yxbh/GridDogs/renders/anchor_bone.png

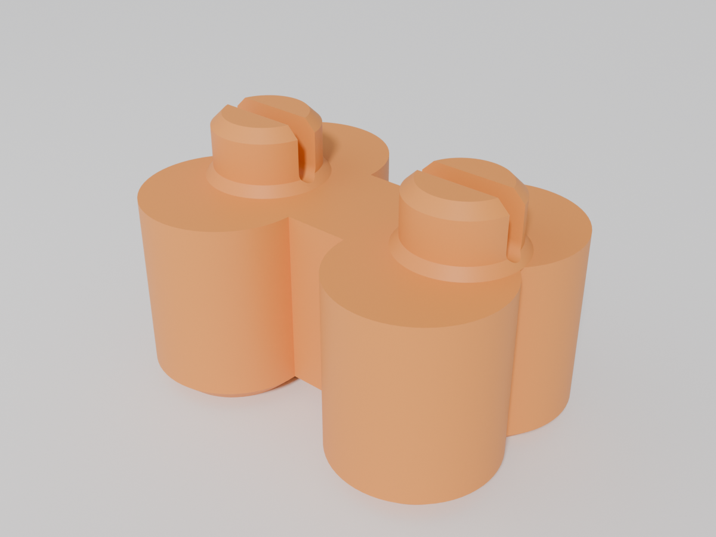
renders/anchor_bone.png
