yxbh/GridDogs/renders/anchor_curve_bowl_20mm.png

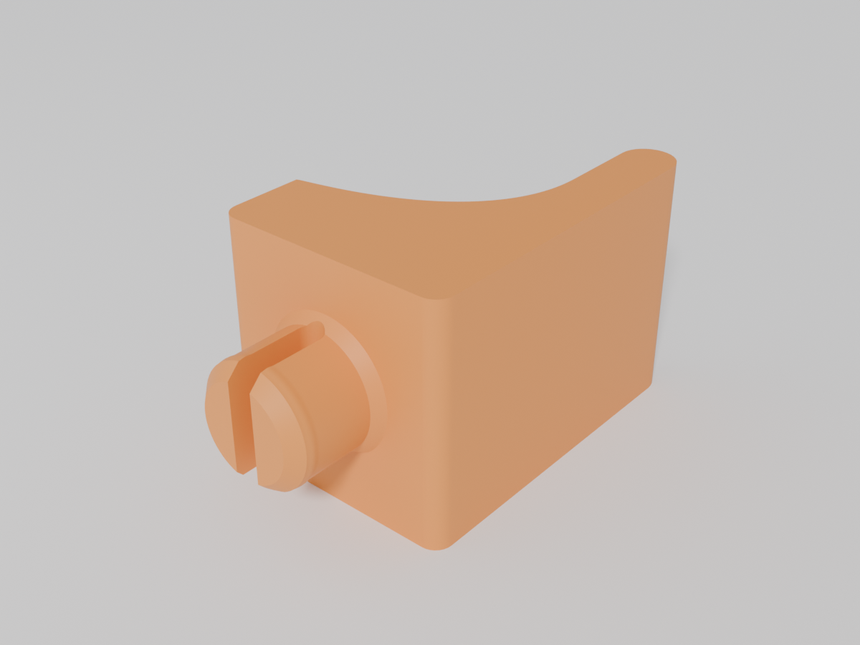
renders/anchor_curve_bowl_20mm.png
