yxbh/GridDogs/renders/anchor_curve_bowl_40mm.png

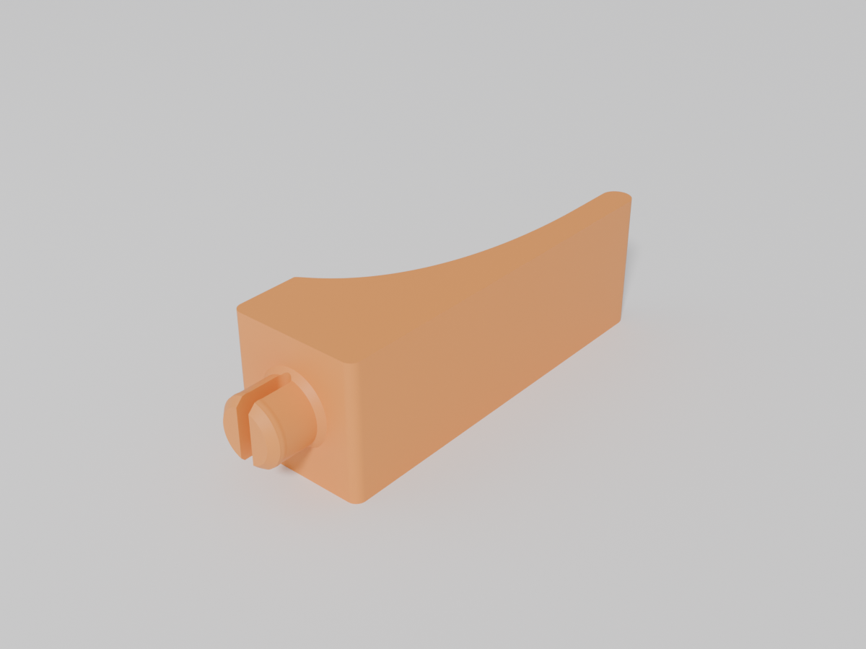
renders/anchor_curve_bowl_40mm.png
