yxbh/GridDogs/renders/anchor_round_bumper_20mm.png

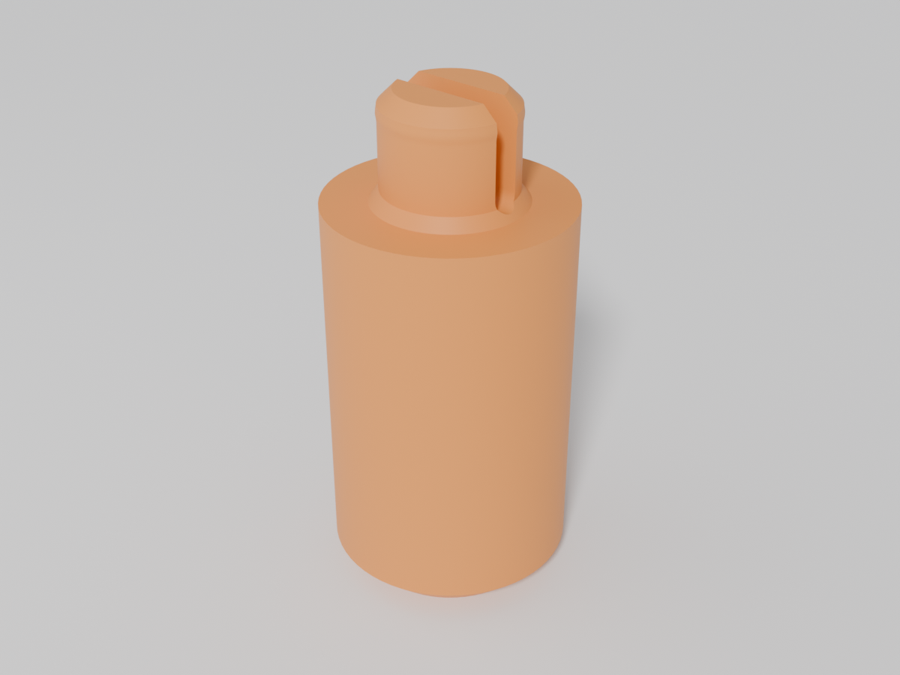
renders/anchor_round_bumper_20mm.png
