yxbh/GridDogs/renders/anchor_round_bumper_40mm.png

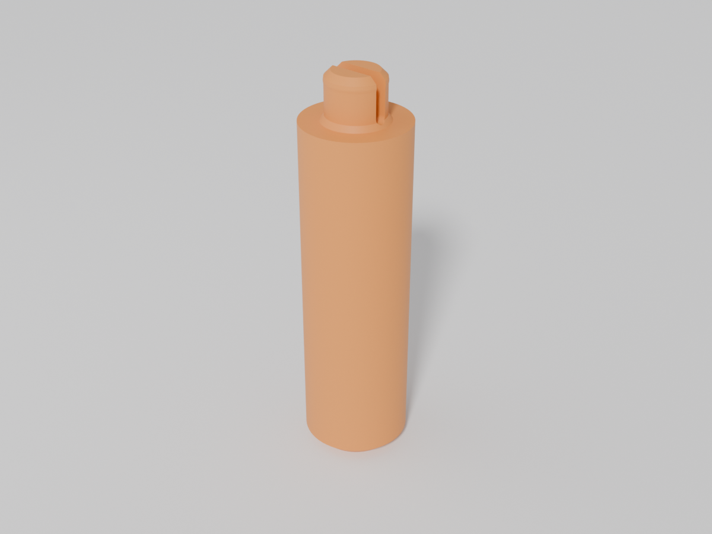
renders/anchor_round_bumper_40mm.png
