yxbh/GridDogs/renders/anchor_wall_diagonal_2x2_20mm.png

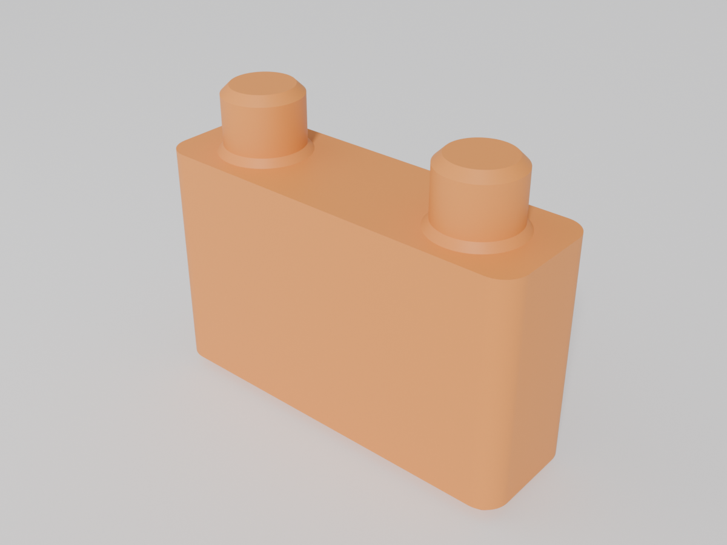
renders/anchor_wall_diagonal_2x2_20mm.png
