yxbh/GridDogs/renders/anchor_wall_diagonal_2x3_40mm.png

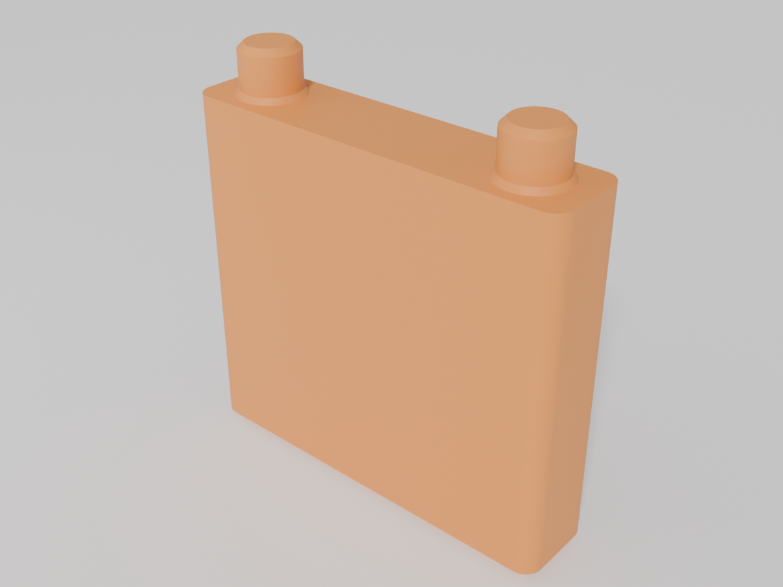
renders/anchor_wall_diagonal_2x3_40mm.png
