yxbh/GridDogs/renders/anchor_wall_long_40mm.png

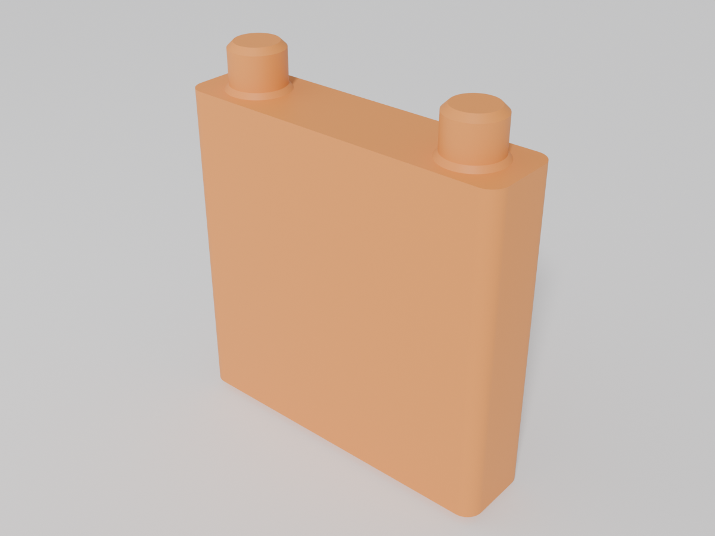
renders/anchor_wall_long_40mm.png
