yxbh/GridDogs/renders/anchor_wall_short_20mm.png

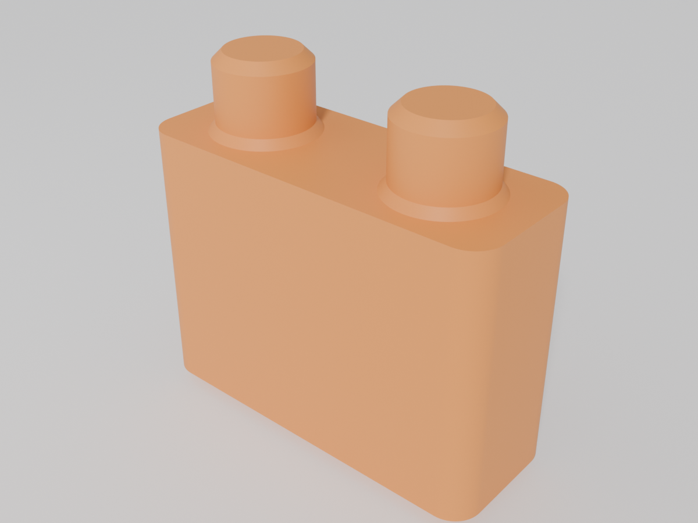
renders/anchor_wall_short_20mm.png
