yxbh/GridDogs/renders/anchor_wall_short_40mm.png

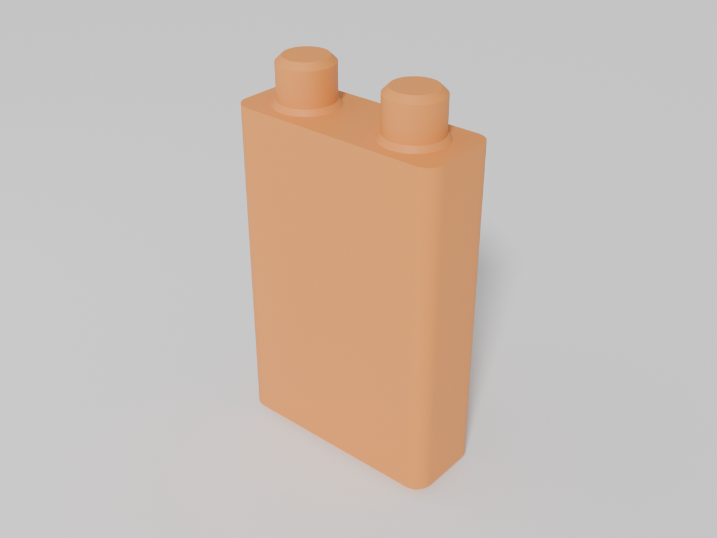
renders/anchor_wall_short_40mm.png
