yxbh/GridDogs/renders/tile_1x1_gridfinity.png

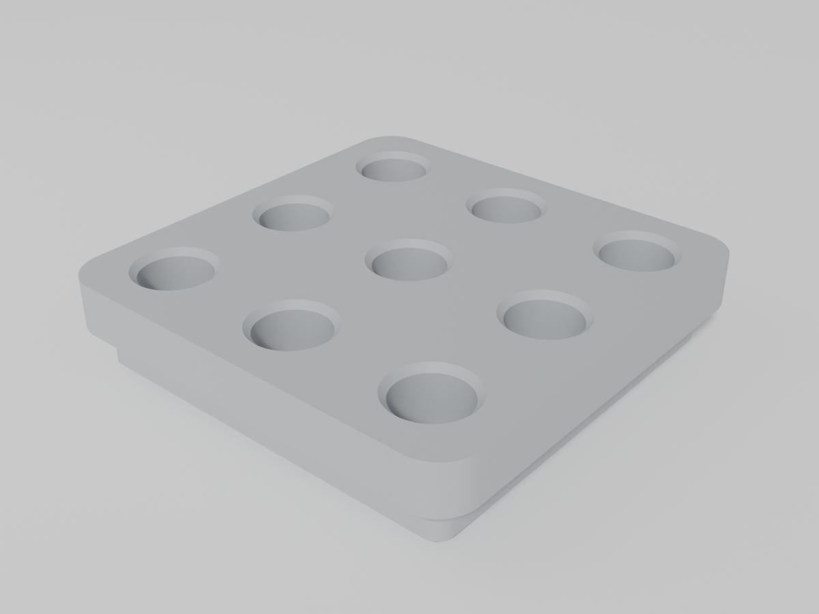
renders/tile_1x1_gridfinity.png
