yxbh/GridDogs/renders/tile_1x3_gridfinity.png

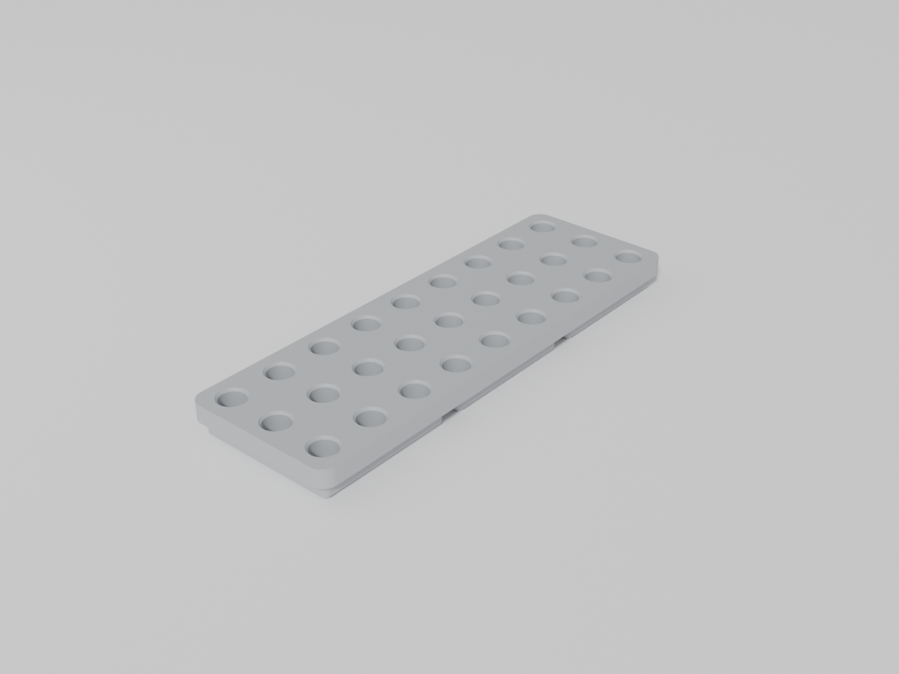
renders/tile_1x3_gridfinity.png
