yxbh/GridDogs/renders/tile_1x7_gridfinity.png

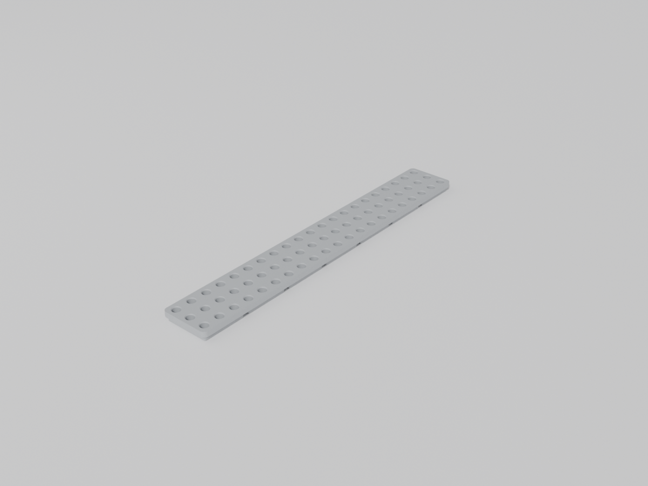
renders/tile_1x7_gridfinity.png
