yxbh/GridDogs/renders/tile_2x2_gridfinity.png

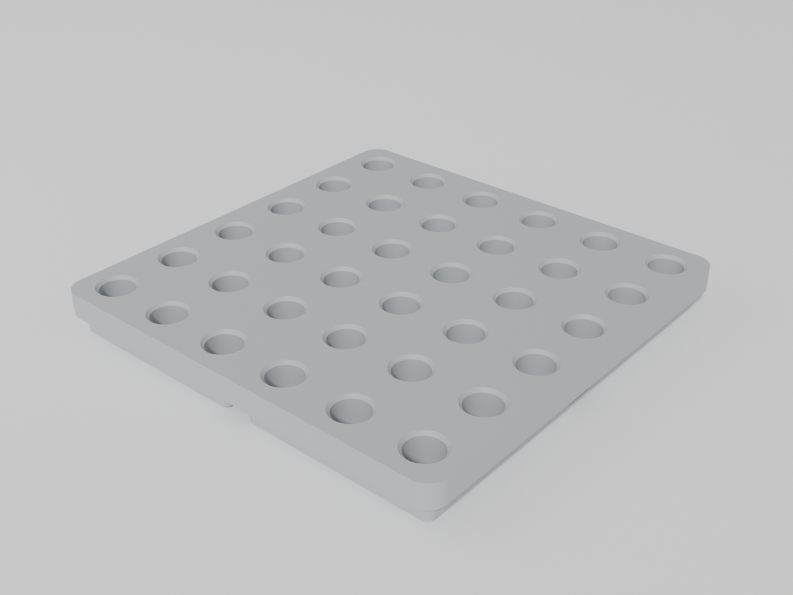
renders/tile_2x2_gridfinity.png
