yxbh/GridDogs/renders/tile_4x4_gridfinity.png

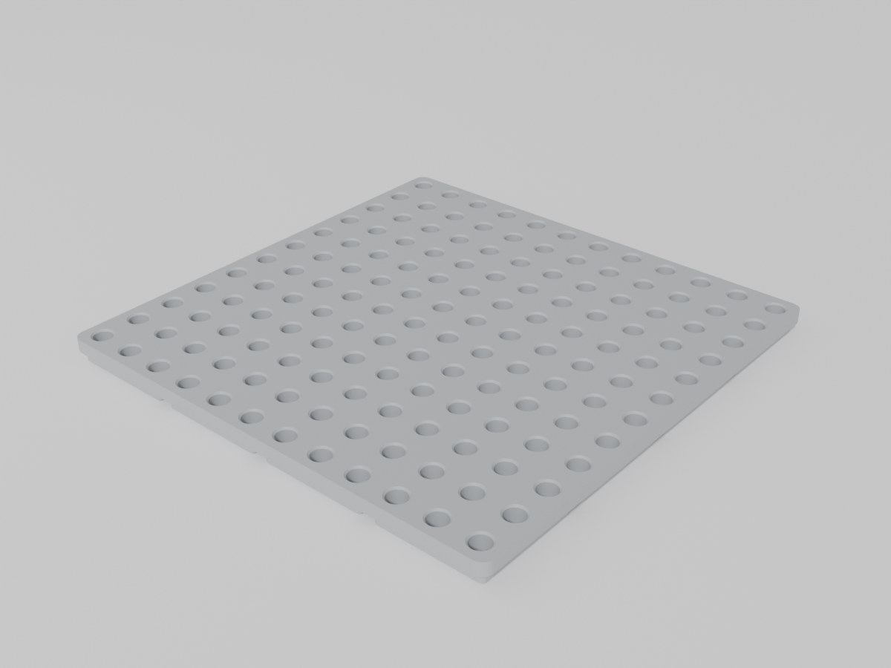
renders/tile_4x4_gridfinity.png
