yxbh/GridDogs/renders/tile_4x7_gridfinity.png

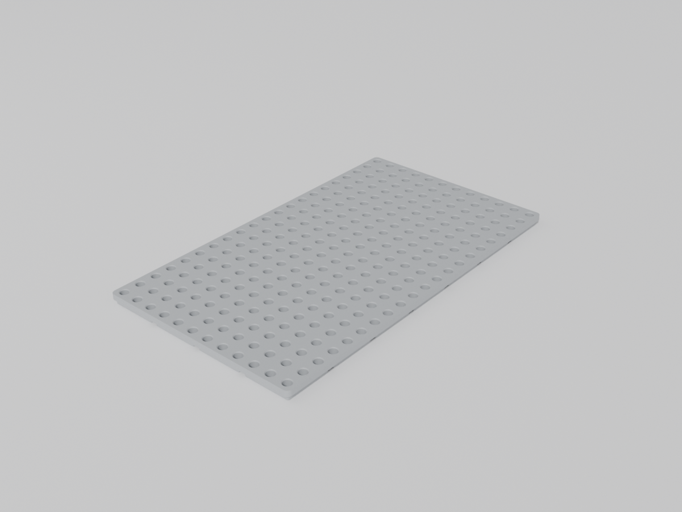
renders/tile_4x7_gridfinity.png
