yxbh/GridDogs/stl/tile_1x1_gridfinity.stl

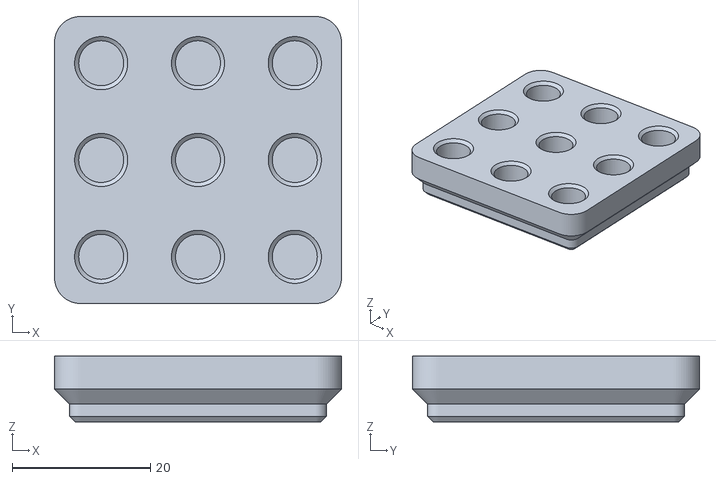
[picture p36: CAD file, 2026-09-03]
stl/tile_1x1_gridfinity.stl
41.5 x 41.5 x 9.50
