yxbh/GridDogs/stl/tile_2x3_gridfinity.stl

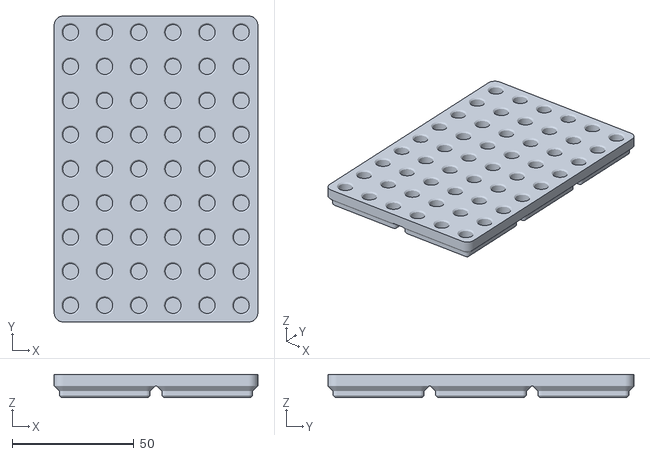
[picture p37: CAD file, 2026-09-03]
stl/tile_2x3_gridfinity.stl
83.5 x 125.5 x 9.50
