yxbh/GridDogs/stl/tile_6x7_gridfinity.stl

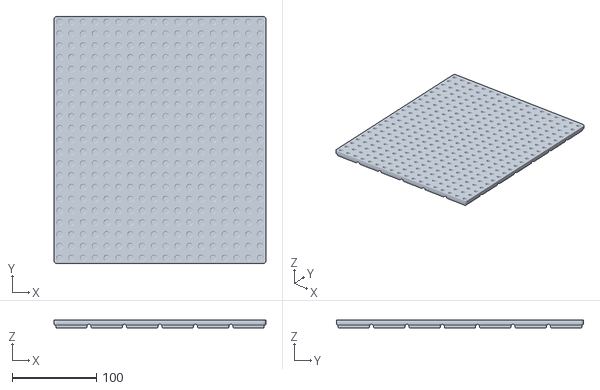
[picture p38: CAD file, 2026-09-03]
stl/tile_6x7_gridfinity.stl
251.5 x 293.5 x 9.50
