yxbh/GridDogs/stl/tile_6x6_gridfinity.stl

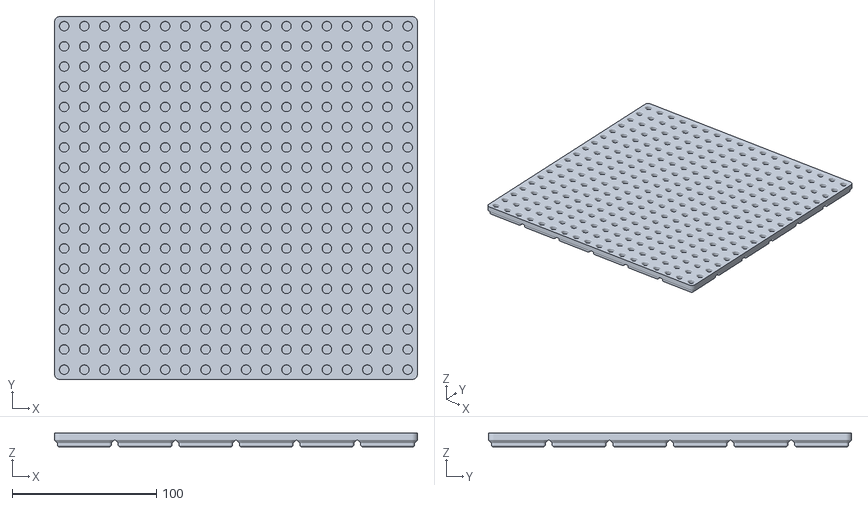
[picture p39: CAD file, 2026-09-03]
stl/tile_6x6_gridfinity.stl
251.5 x 251.5 x 9.50
