yxbh/GridDogs/stl/tile_4x4_gridfinity.stl

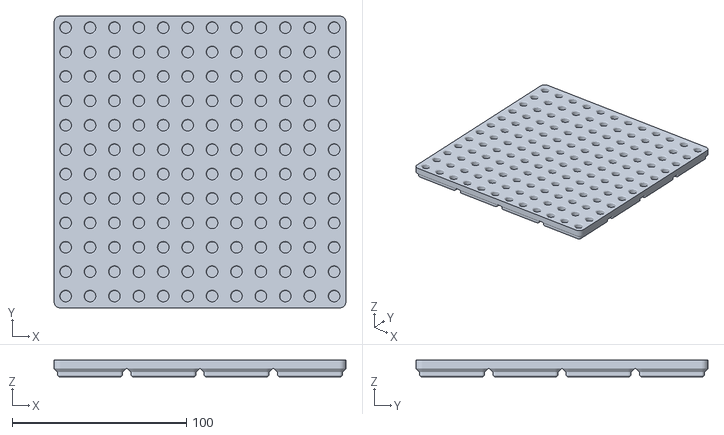
[picture p40: CAD file, 2026-09-03]
stl/tile_4x4_gridfinity.stl
167.5 x 167.5 x 9.50
