yxbh/GridDogs/stl/tile_1x4_gridfinity.stl

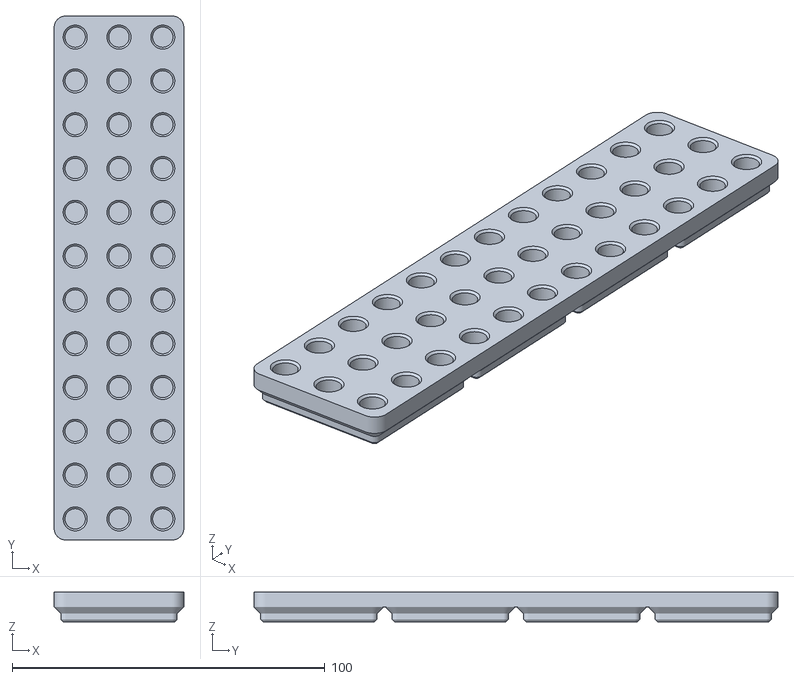
[picture p41: CAD file, 2026-09-03]
stl/tile_1x4_gridfinity.stl
41.5 x 167.5 x 9.50
