yxbh/GridDogs/stl/tile_1x6_gridfinity.stl

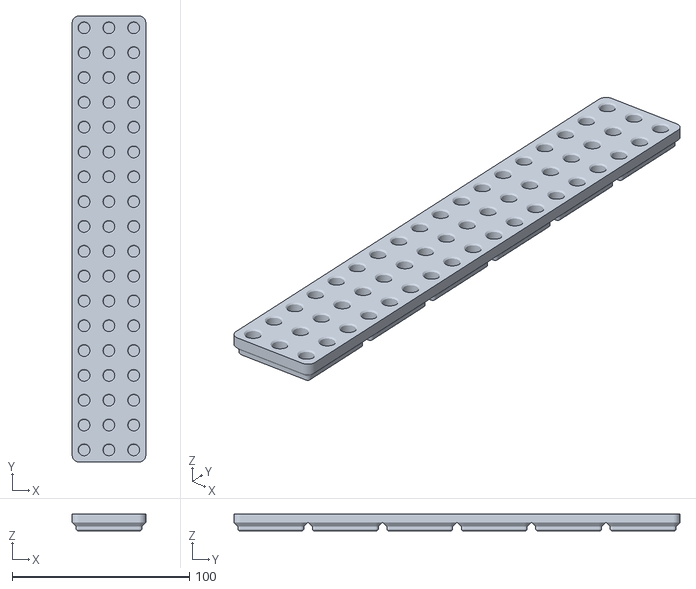
[picture p42: CAD file, 2026-09-03]
stl/tile_1x6_gridfinity.stl
41.5 x 251.5 x 9.50
