yxbh/GridDogs/stl/anchor_round_bumper_40mm.stl

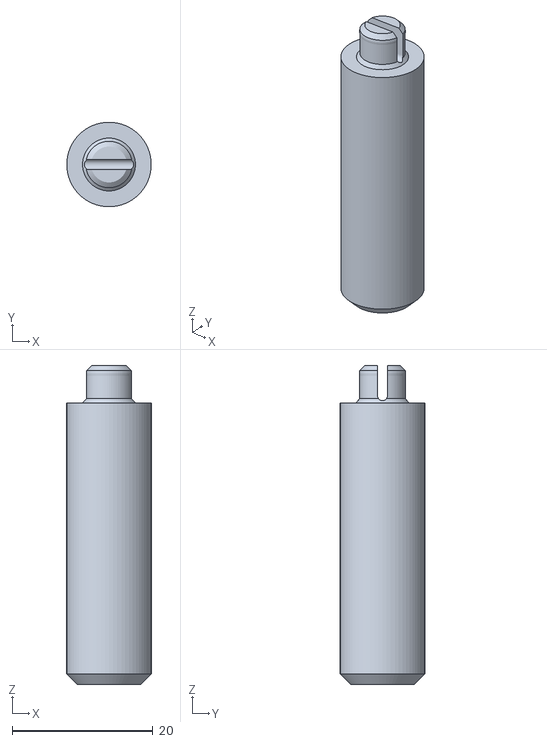
[picture p43: CAD file, 2026-09-03]
stl/anchor_round_bumper_40mm.stl
12.0 x 12.0 x 45.3
