yxbh/GridDogs/stl/tile_1x3_gridfinity.stl

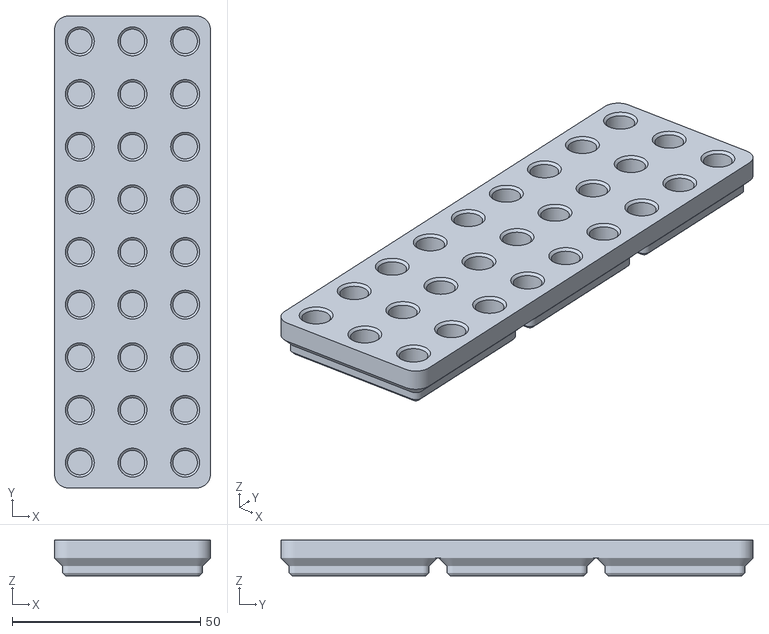
[picture p44: CAD file, 2026-09-03]
stl/tile_1x3_gridfinity.stl
41.5 x 125.5 x 9.50
