yxbh/GridDogs/stl/tile_7x7_gridfinity.stl

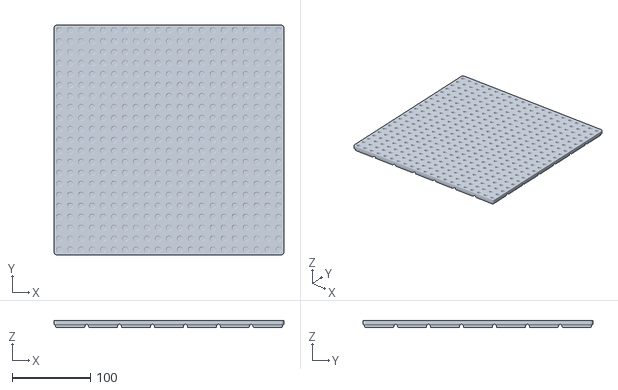
[picture p45: CAD file, 2026-09-03]
stl/tile_7x7_gridfinity.stl
293.5 x 293.5 x 9.50
