yxbh/GridDogs/stl/tile_3x4_gridfinity.stl

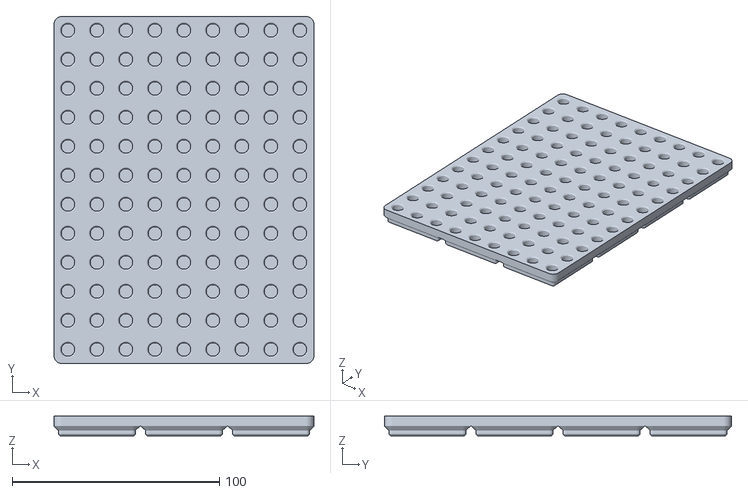
[picture p46: CAD file, 2026-09-03]
stl/tile_3x4_gridfinity.stl
125.5 x 167.5 x 9.50
