yxbh/GridDogs/stl/anchor_round_bumper_20mm.stl

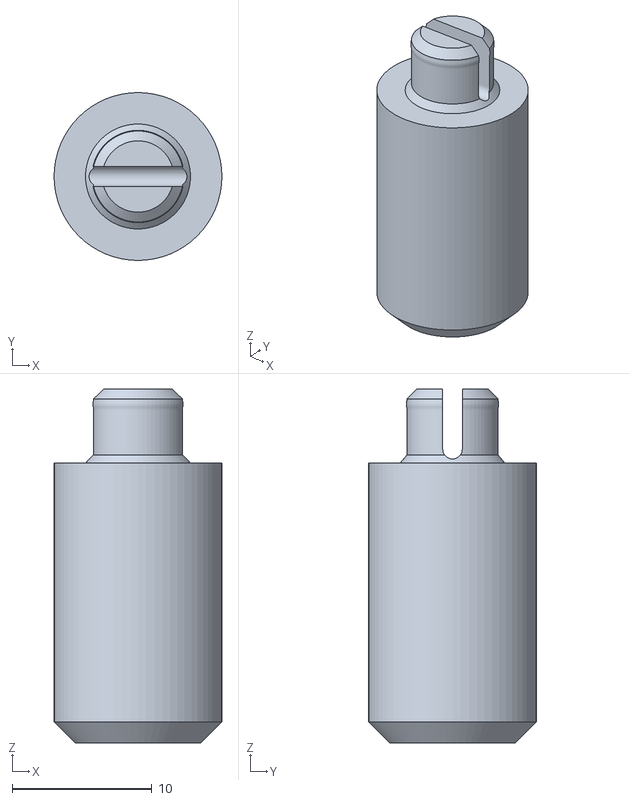
[picture p47: CAD file, 2026-09-03]
stl/anchor_round_bumper_20mm.stl
12.0 x 12.0 x 25.3
