yxbh/GridDogs/stl/tile_3x3_gridfinity.stl

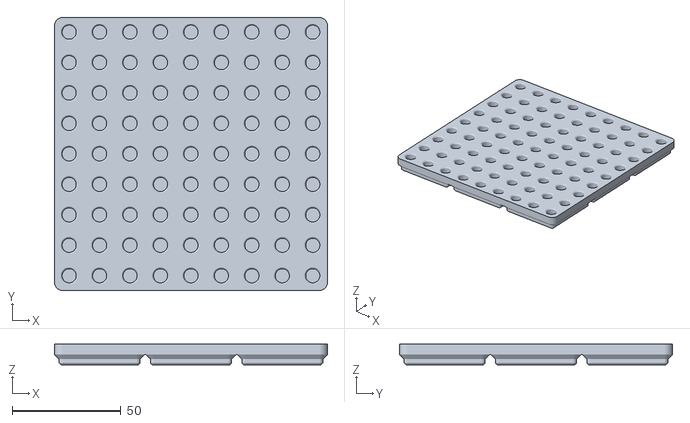
[picture p48: CAD file, 2026-09-03]
stl/tile_3x3_gridfinity.stl
125.5 x 125.5 x 9.50
