yxbh/GridDogs/stl/tile_2x7_gridfinity.stl

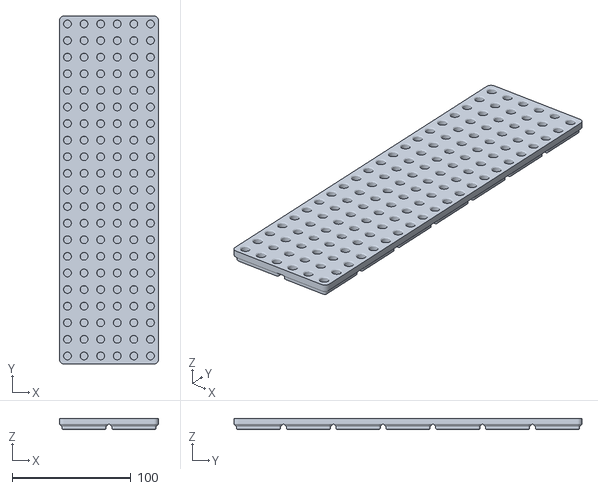
[picture p49: CAD file, 2026-09-03]
stl/tile_2x7_gridfinity.stl
83.5 x 293.5 x 9.50
