yxbh/GridDogs/stl/tile_2x5_gridfinity.stl

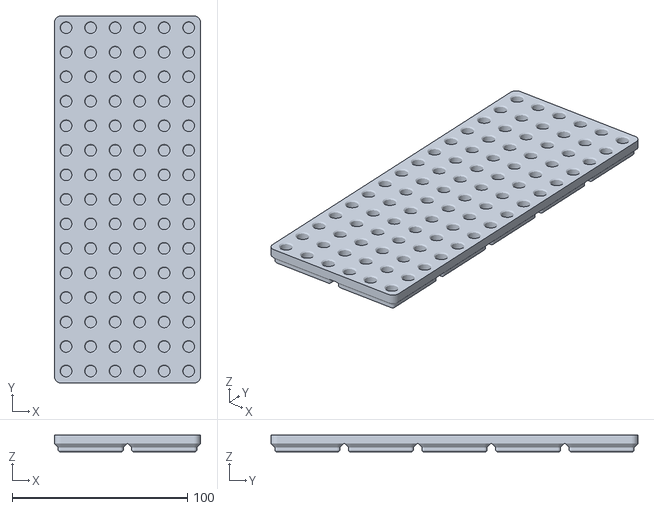
[picture p50: CAD file, 2026-09-03]
stl/tile_2x5_gridfinity.stl
83.5 x 209.5 x 9.50
