yxbh/GridDogs/stl/tile_5x6_gridfinity.stl

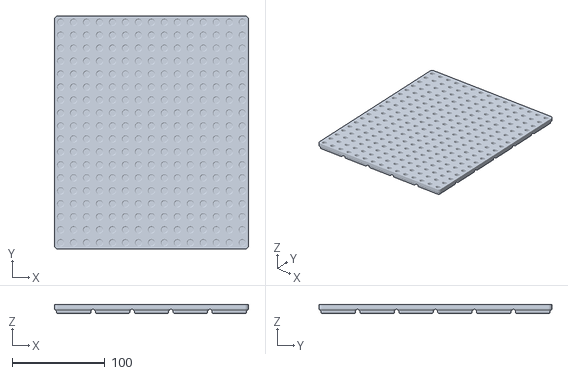
[picture p51: CAD file, 2026-09-03]
stl/tile_5x6_gridfinity.stl
209.5 x 251.5 x 9.50
