yxbh/GridDogs/stl/anchor_wall_long_40mm.stl

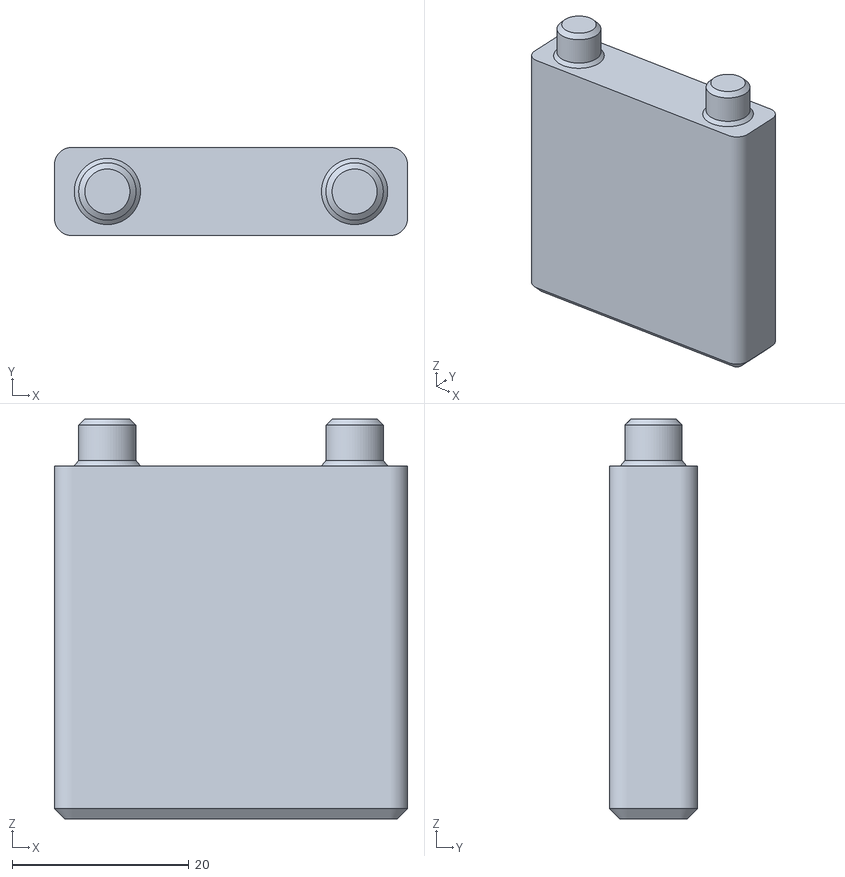
[picture p52: CAD file, 2026-09-03]
stl/anchor_wall_long_40mm.stl
40.0 x 10.0 x 45.3
