yxbh/GridDogs/stl/tile_3x6_gridfinity.stl

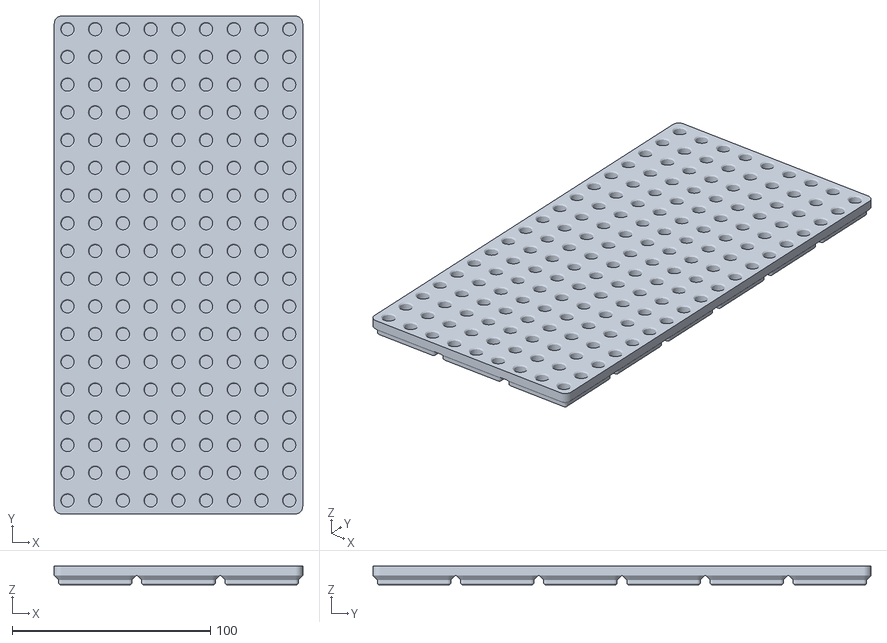
[picture p53: CAD file, 2026-09-03]
stl/tile_3x6_gridfinity.stl
125.5 x 251.5 x 9.50
