yxbh/GridDogs/stl/anchor_curve_standard_40mm.stl

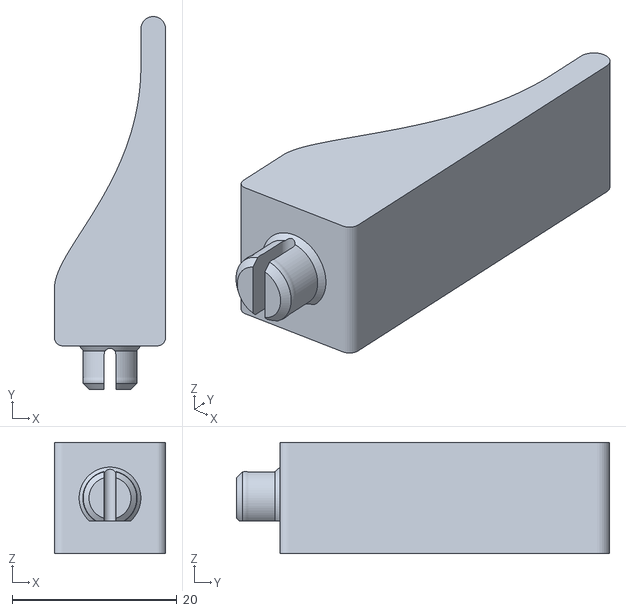
[picture p54: CAD file, 2026-09-03]
stl/anchor_curve_standard_40mm.stl
13.5 x 45.3 x 13.5
