yxbh/GridDogs/stl/tile_3x7_gridfinity.stl

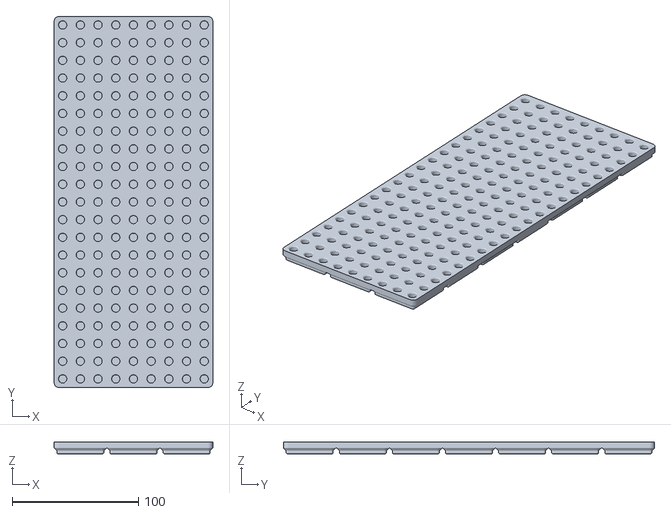
[picture p55: CAD file, 2026-09-03]
stl/tile_3x7_gridfinity.stl
125.5 x 293.5 x 9.50
