yxbh/GridDogs/stl/tile_4x6_gridfinity.stl

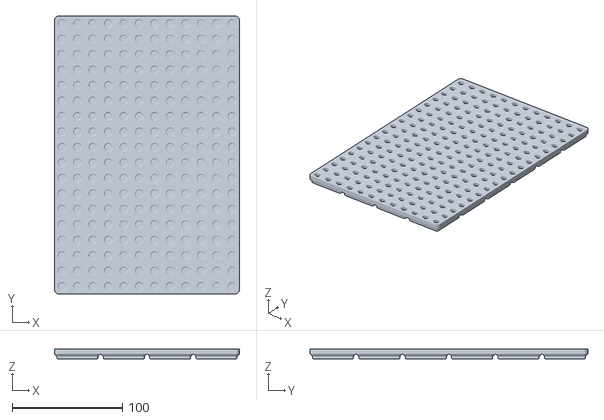
[picture p56: CAD file, 2026-09-03]
stl/tile_4x6_gridfinity.stl
167.5 x 251.5 x 9.50
