yxbh/GridDogs/stl/tile_5x7_gridfinity.stl

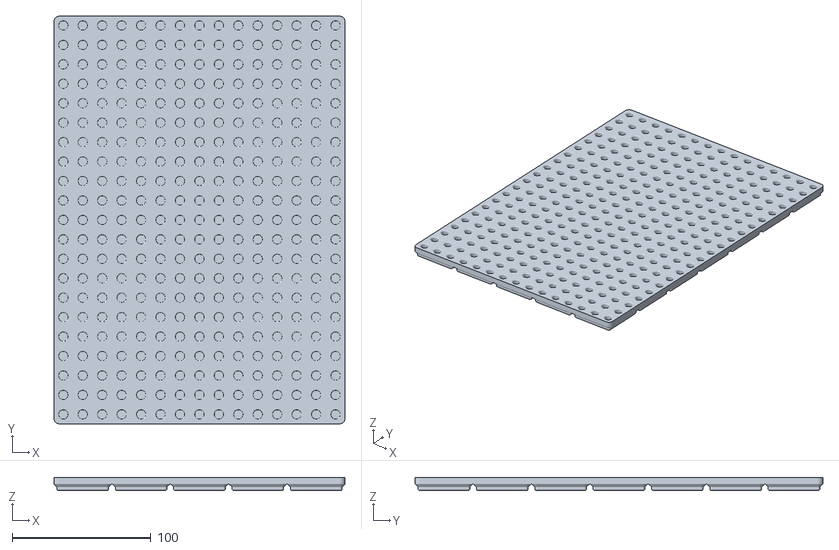
[picture p57: CAD file, 2026-09-03]
stl/tile_5x7_gridfinity.stl
209.5 x 293.5 x 9.50
