yxbh/GridDogs/stl/tile_3x5_gridfinity.stl

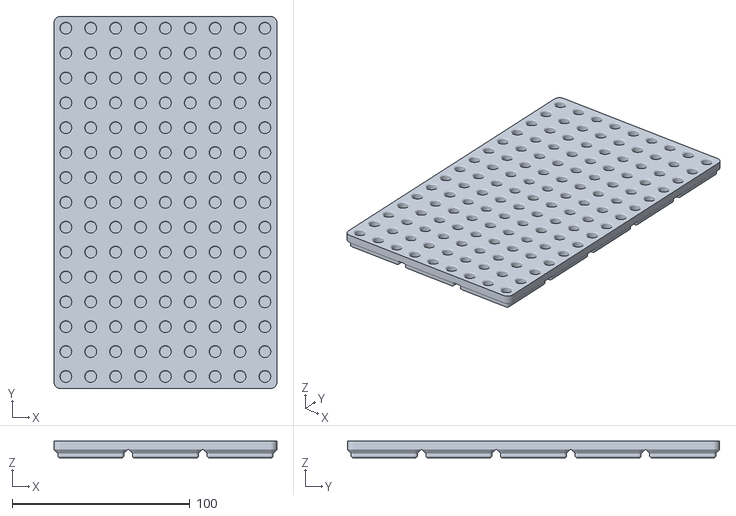
[picture p58: CAD file, 2026-09-03]
stl/tile_3x5_gridfinity.stl
125.5 x 209.5 x 9.50
