yxbh/GridDogs/stl/tile_4x5_gridfinity.stl

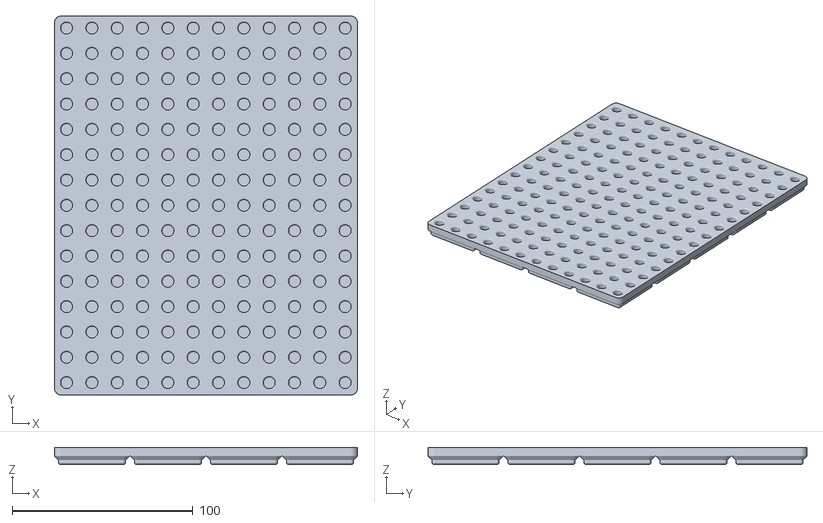
[picture p59: CAD file, 2026-09-03]
stl/tile_4x5_gridfinity.stl
167.5 x 209.5 x 9.50
