yxbh/GridDogs/stl/tile_2x4_gridfinity.stl

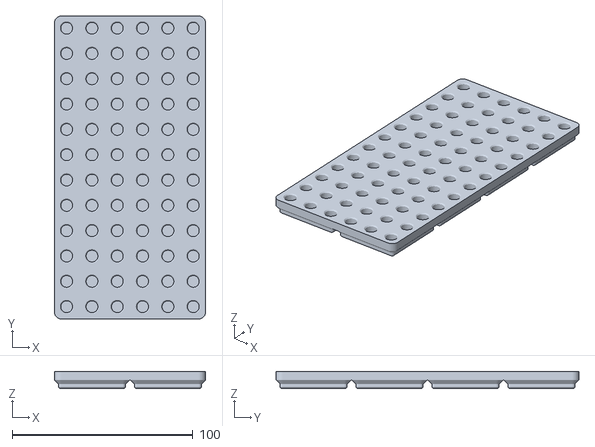
[picture p60: CAD file, 2026-09-03]
stl/tile_2x4_gridfinity.stl
83.5 x 167.5 x 9.50
