yxbh/GridDogs/stl/anchor_wall_short_20mm.stl

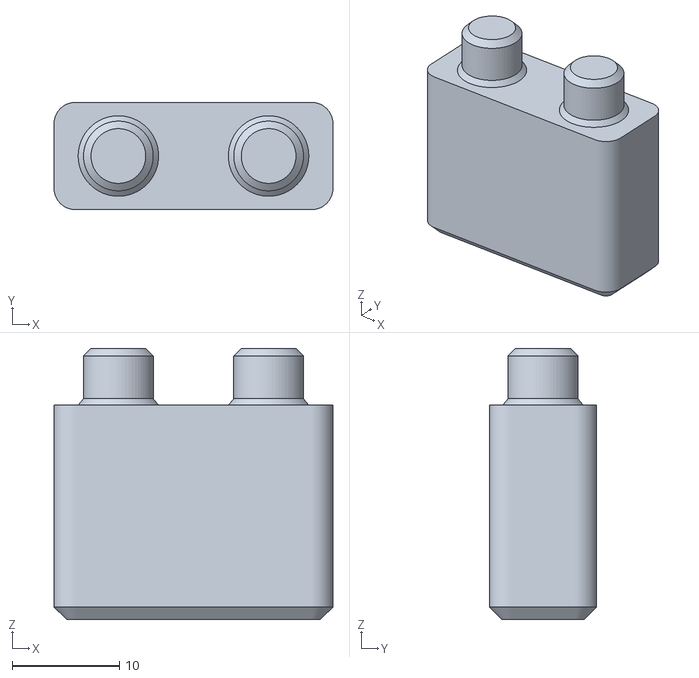
[picture p61: CAD file, 2026-09-03]
stl/anchor_wall_short_20mm.stl
26.0 x 10.0 x 25.3
