yxbh/GridDogs/stl/anchor_wall_long_20mm.stl

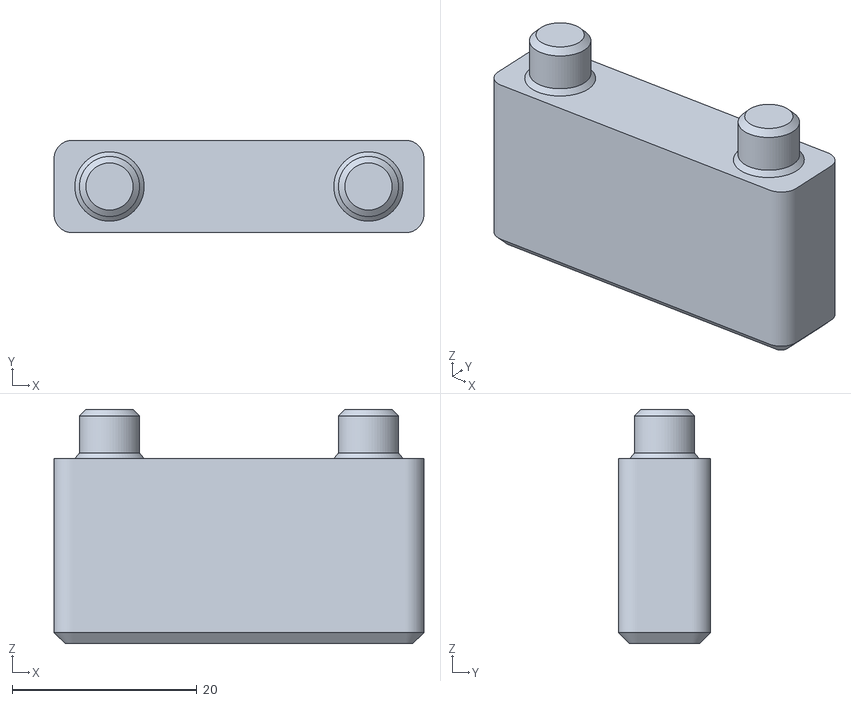
[picture p62: CAD file, 2026-09-03]
stl/anchor_wall_long_20mm.stl
40.0 x 10.0 x 25.3
