yxbh/GridDogs/stl/anchor_bone.stl

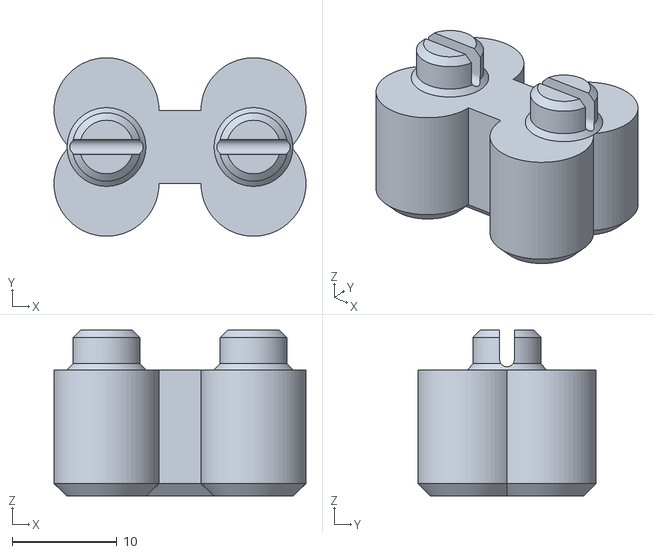
[picture p63: CAD file, 2026-09-03]
stl/anchor_bone.stl
24.0 x 17.0 x 15.8
