yxbh/GridDogs/stl/fit_test_coupon.stl

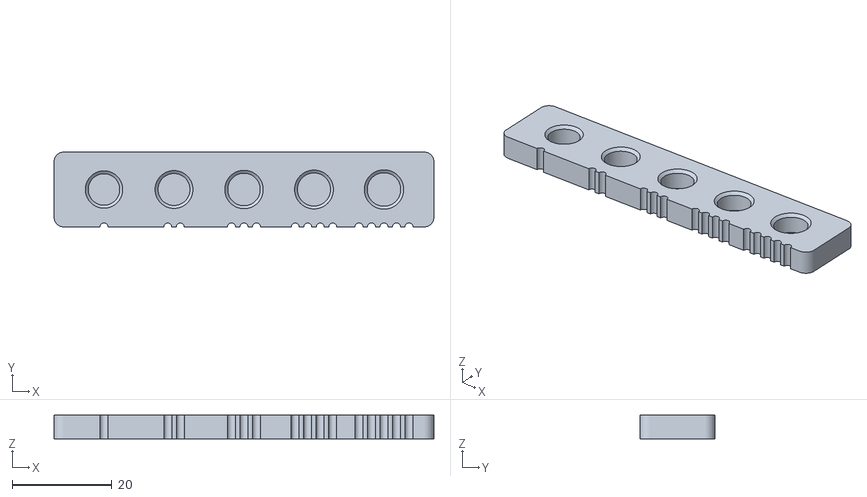
[picture p64: CAD file, 2026-08-23]
stl/fit_test_coupon.stl
76.0 x 15.0 x 4.75
