yxbh/GridDogs/renders/fit_test_coupon.png

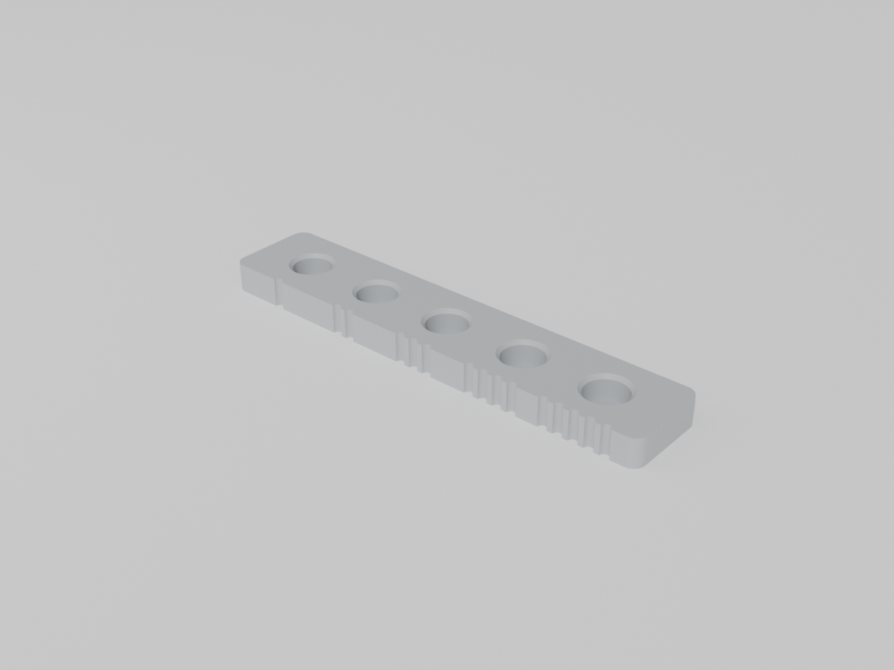
renders/fit_test_coupon.png
